fengyenchia/tiger-camera/firmware/tiger-camera-v1/include/r2_root_ca.h

#pragma once

// Public trust anchor for the currently observed Cloudflare R2 chain:
//   <account>.r2.cloudflarestorage.com -> WE1 -> GTS Root R4
// Source: https://pki.goog/roots.pem
// SHA-256: 349DFA4058C5E263123B398AE795573C4E1313C83FE68F93556CD5E8031B3C7D
// Valid until: 2036-06-22. Re-check the live R2 chain before that date and
// whenever Cloudflare changes certificate authorities.
constexpr char r2TlsRootCaPem[] = R"PEM(
-----BEGIN CERTIFICATE-----
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
-----END CERTIFICATE-----
)PEM";
